BrettHallen/BIT90_26/KiCad/BIT90_Scraps/BIT90_Clocks.jpg

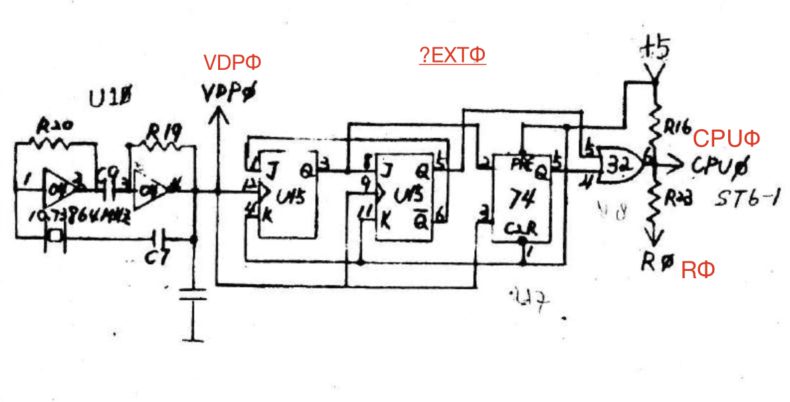
KiCad/BIT90_Scraps/BIT90_Clocks.jpg
